lorcan2440/EIT_Touch_Sensor/Papers/urop_paper/Images/Figure_1_diagram.pdf

②

①

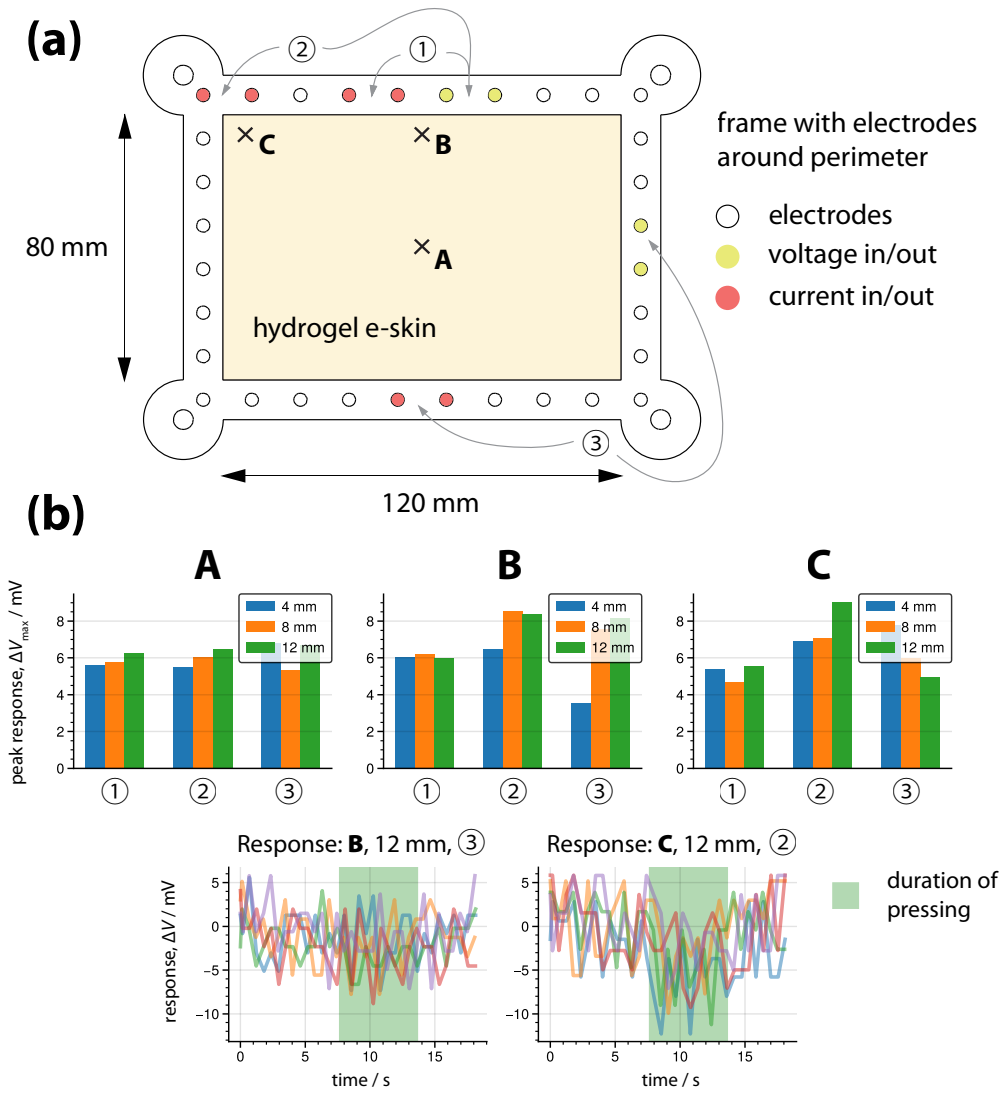
[picture p15: page 1]
hydrogel e-skin; Response:; time / s; response, ∆V / mV; duration of pressing

frame with electrodes
around perimeter
electrodes
voltage in/out
current in/out

peak response, ∆Vmax / mV
